atiq-mufaqqir/TinyML-Environmental-Hazard-Monitor/TEST.ioc

Mcu.UserName=STM32L476RGTx
PA2.GPIO_Label=USART_TX
PA2.Signal=USART2_TX
PA3.GPIO_Label=USART_RX
PA3.Signal=USART2_RX
PA5.GPIO_Label=LD2 [green Led]
PA5.Signal=GPIO_Output
PB8.Signal=I2C1_SCL
PB9.Signal=I2C1_SDA
PC13.GPIO_Label=B1 [Blue PushButton]
PC13.Signal=GPXTI13
